nitinyadaviitr/Electronic-Toilet-Usage-Monitoring/ETUM-Swachathon/Price/1M.PNG

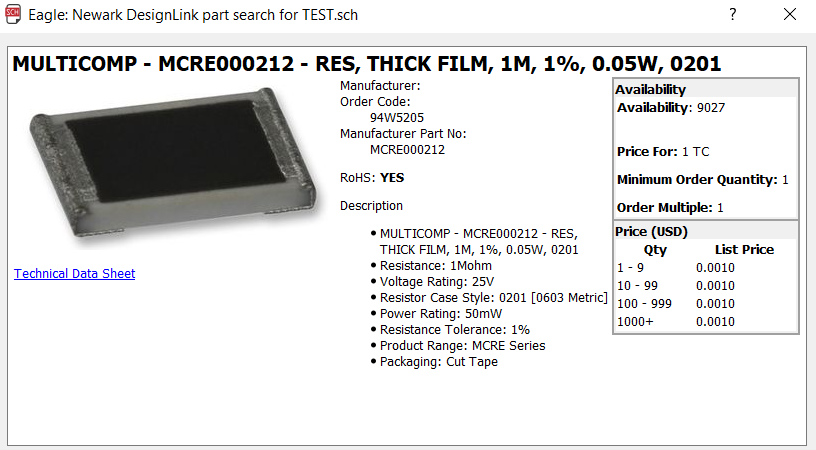
ETUM-Swachathon/Price/1M.PNG
