nitinyadaviitr/Electronic-Toilet-Usage-Monitoring/ETUM-Swachathon/Price/10nF.PNG

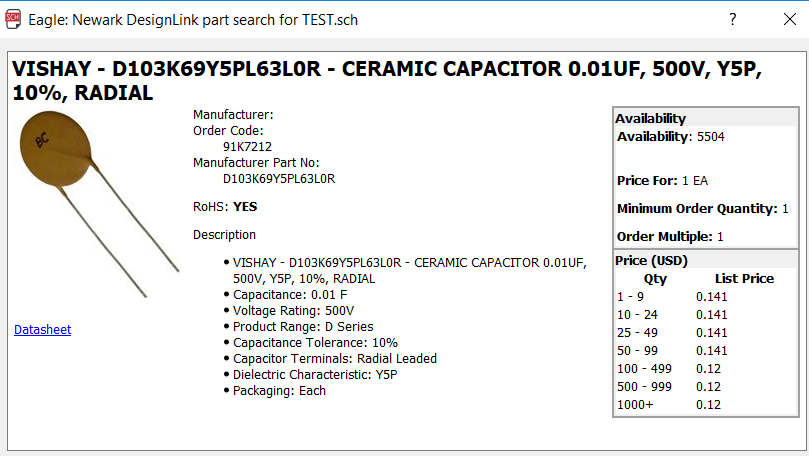
ETUM-Swachathon/Price/10nF.PNG
