nitinyadaviitr/Electronic-Toilet-Usage-Monitoring/ETUM-Swachathon/Price/18kohm.PNG

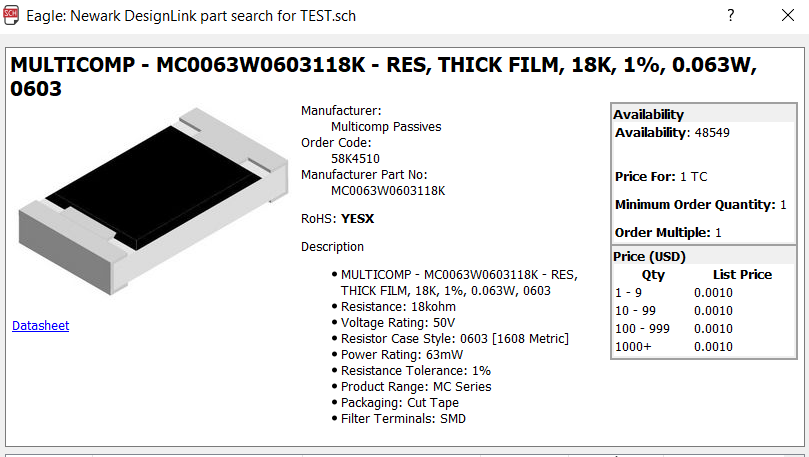
ETUM-Swachathon/Price/18kohm.PNG
