nitinyadaviitr/Electronic-Toilet-Usage-Monitoring/ETUM-Swachathon/Price/47kohm.PNG

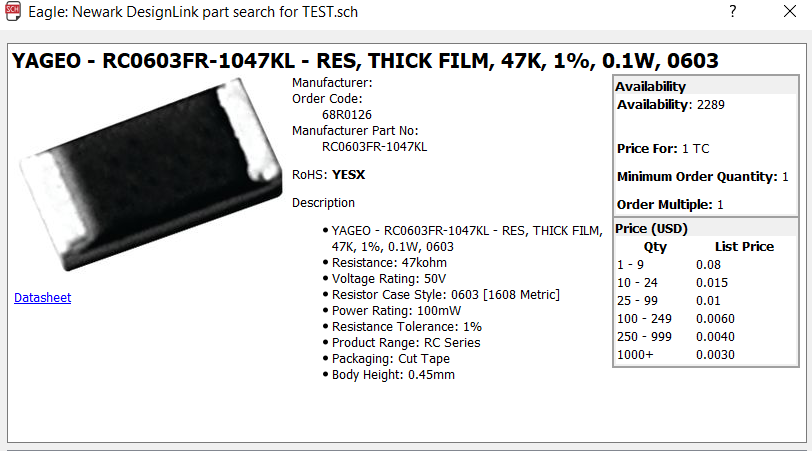
ETUM-Swachathon/Price/47kohm.PNG
