nitinyadaviitr/Electronic-Toilet-Usage-Monitoring/ETUM-Swachathon/Price/47uF.PNG

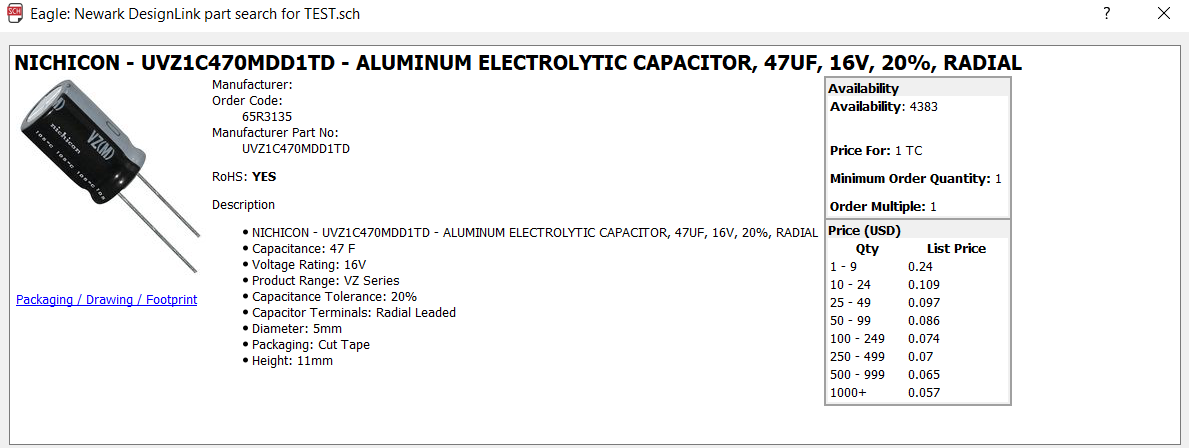
ETUM-Swachathon/Price/47uF.PNG
